mattybrad/polymod/teensymodsynth/Envelope.cpp

#include "Arduino.h"
#include "Envelope.h"
#include "Socket.h"

Envelope::Envelope() {
  _dc.amplitude(1.0);
  _envelope.attack(100);
  _envelope.release(2000);
  _patchCable1 = new AudioConnection(_dc,0,_envelope,0);
  _queue.begin();
  sockets[5].setInput(_queue, 0); // gate
  sockets[2].setOutput(_envelope, 0); // audio out
  // to do: add retrigger function on socket 1
}

void Envelope::update() {
  _envelope.attack(1000*controls[4].getSmoothedValue());
  _envelope.decay(1000*controls[6].getSmoothedValue());
  _envelope.sustain(controls[7].getSmoothedValue());
  _envelope.release(2000*controls[5].getSmoothedValue());
  if(_queue.available() > 0) {
    int16_t test[128];
    memcpy(test, _queue.readBuffer(), 256);
    _queue.freeBuffer();
    int16_t x = test[0];
    boolean newGateReading = (x > 0);
    if(newGateReading != _gateOpen) {
      _gateOpen = newGateReading;
      if(_gateOpen) _envelope.noteOn();
      else _envelope.noteOff();
    }
    _queue.clear();
  }
}
